DonVasyl/SyncBlaster/boards/SyncBlaster_prototype_000/SyncBlaster_prototype.kicad_sch

## KiCad design boards/SyncBlaster_prototype_000/SyncBlaster_prototype.kicad_sch (2024-04-04)

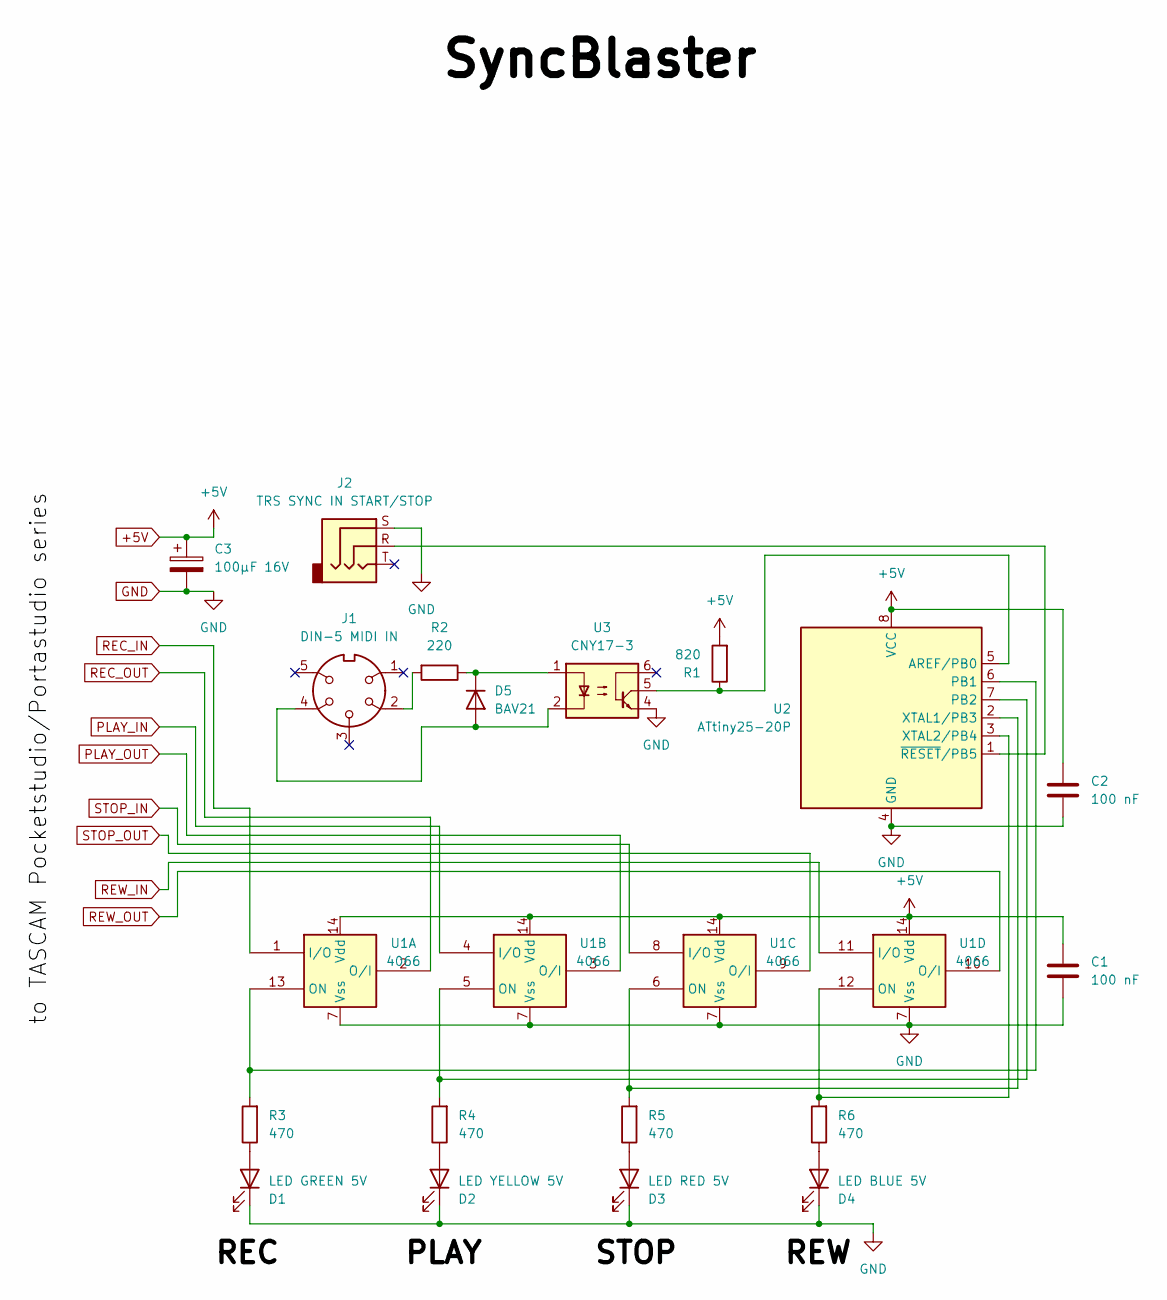
[picture p2: schematic SyncBlaster_prototype.kicad_sch]

Parts:
C1, C2: 100 nF
C3: 100µF 16V
D1: LED GREEN 5V
D2: LED YELLOW 5V
D3: LED RED 5V
D4: LED BLUE 5V
D5: BAV21; D_DO-35_SOD27_P7.62mm_Horizontal
J1: DIN-5 MIDI IN
J2: TRS SYNC IN START/STOP
R1: 820
R2: 220
R3, R4, R5, R6: 470
U1: 4066
U2: ATtiny25-20P; DIP-8_W7.62mm
U3: CNY17-3

Connections:
+5V: C1.1, C2.1, C3.1, R1.2, U1.14 (Vdd), U2.8 (VCC)
GND: C1.2, C2.2, C3.2, D1.1 (K), D2.1 (K), D3.1 (K), D4.1 (K), J2.S, U1.7 (Vss), U2.4 (GND), U3.4
unnamed: D1.2 (A), R3.1
unnamed: D2.2 (A), R4.1
unnamed: D3.2 (A), R5.1
unnamed: D4.2 (A), R6.1
unnamed: D5.1 (K), R2.1, U3.1
unnamed: D5.2 (A), J1.4, U3.2
unnamed: J1.2, R2.2
unnamed: J2.R, U2.1 (~RESET/PB5)
unnamed: R1.1, U2.5 (AREF/PB0), U3.5
unnamed: R3.2, U1.13 (ON), U2.6 (PB1)
unnamed: R4.2, U1.5 (ON), U2.7 (PB2)
unnamed: R5.2, U1.6 (ON), U2.2 (XTAL1/PB3)
unnamed: R6.2, U1.12 (ON), U2.3 (XTAL2/PB4)
PLAY_IN: U1.4 (I/O)
PLAY_OUT: U1.3 (O/I)
REC_IN: U1.1 (I/O)
REC_OUT: U1.2 (O/I)
REW_IN: U1.11 (I/O)
REW_OUT: U1.10 (O/I)
STOP_IN: U1.8 (I/O)
STOP_OUT: U1.9 (O/I)
